iley/kamaji/demos/lcd/src/main.cpp

/*
  LiquidCrystal Library - Hello World
 
 Demonstrates the use a 16x2 LCD display.  The LiquidCrystal
 library works with all LCD displays that are compatible with the 
 Hitachi HD44780 driver. There are many of them out there, and you
 can usually tell them by the 16-pin interface.
 
 This sketch prints "Hello World!" to the LCD
 and shows the time.
 
  The circuit:
 * LCD RS pin to digital pin 12
 * LCD RW pin to digital pin 10
 * LCD Enable pin to digital pin 11
 * LCD D4 pin to digital pin 5
 * LCD D5 pin to digital pin 4
 * LCD D6 pin to digital pin 3
 * LCD D7 pin to digital pin 2
 * 10K resistor:
 * ends to +5V and ground
 * wiper to LCD VO pin (pin 3)
 
 Library originally added 18 Apr 2008
 by David A. Mellis
 library modified 5 Jul 2009
 by Limor Fried (http://www.ladyada.net)
 example added 9 Jul 2009
 by Tom Igoe
 modified 25 July 2009
 by David A. Mellis
 modified 25 May 2010
 by Ilya V. Danilov http://mk90.ru/

 */

// include the library code:
#include "Arduino.h"
#include <Wire.h>
#include <LiquidCrystal.h>

// initialize the library with the numbers of the interface pins
LiquidCrystal lcd(12, 11, 10, 9, 8, 7, 6);

void setup() {
  // set up the LCD's number of rows and columns: 
  lcd.begin(20, 4);
  // Print a message to the LCD.
  lcd.print("Привет, мир!");
}

void loop() {
  // set the cursor to column 0, line 1
  // (note: line 1 is the second row, since counting begins with 0):
  //lcd.setCursor(0, 1);
  // print the number of seconds since reset:
  lcd.print(millis()/1000);
  for (int k = 0; k < 5; k++) {
    for (int i = 0; i < 20; i++) {
      for (int j = 0; j < 4; j++) {
        if (k*80+j*20+i > 255)
          break;
        lcd.setCursor(i, j);
        lcd.write((unsigned char)(k*80 + j*20 + i));
      }
    }
    delay(2000);
  }
}
