iley/kamaji/demos/lcd12864/src/bitmap.h

#ifndef BITMAP_H
#define BITMAP_H

#define BITMAP_WIDTH 128
#define BITMAP_HEIGHT 64

#define BITMAP_DATA \
  0x00, 0x00, 0xC0, 0x00, 0x00, 0x00, 0x00, 0x00, 0x00, 0x00, 0x00, 0x00, \
  0x00, 0x00, 0x00, 0x00, 0x00, 0x00, 0xE0, 0x03, 0x00, 0x00, 0x00, 0x00, \
  0x00, 0x00, 0x00, 0x00, 0x00, 0x00, 0x00, 0x00, 0x00, 0x00, 0xF0, 0x03, \
  0x00, 0x00, 0x00, 0x00, 0x00, 0x00, 0x00, 0x00, 0x00, 0x00, 0x00, 0x00, \
  0x00, 0x00, 0x78, 0x06, 0x00, 0x00, 0x00, 0x00, 0x00, 0x00, 0x00, 0x00, \
  0x00, 0x00, 0x00, 0x00, 0x00, 0x00, 0x78, 0x0F, 0x00, 0x00, 0x00, 0x00, \
  0x00, 0x00, 0x00, 0x00, 0x00, 0x00, 0x00, 0x00, 0x00, 0x00, 0x78, 0x0C, \
  0x00, 0x00, 0x00, 0x00, 0x00, 0x00, 0x00, 0x00, 0x00, 0x00, 0x00, 0x00, \
  0x00, 0x00, 0x78, 0x1A, 0x00, 0x00, 0x00, 0x00, 0x00, 0x00, 0x00, 0x00, \
  0x00, 0x00, 0x00, 0x00, 0x78, 0x00, 0x98, 0x38, 0x00, 0x00, 0x00, 0x00, \
  0x00, 0x00, 0x00, 0x00, 0x00, 0x00, 0x00, 0x00, 0xFC, 0x00, 0x5C, 0x39, \
  0x00, 0x00, 0x00, 0x00, 0x00, 0x00, 0x00, 0x00, 0x00, 0x00, 0x00, 0x00, \
  0xDC, 0x01, 0x48, 0x72, 0x00, 0x00, 0x00, 0x00, 0x00, 0x00, 0x00, 0x00, \
  0x00, 0x00, 0x00, 0x00, 0x9C, 0x01, 0x58, 0x60, 0x00, 0x00, 0xF0, 0x03, \
  0x00, 0x00, 0x00, 0x00, 0x00, 0x00, 0x00, 0x00, 0xBE, 0x03, 0x9C, 0x62, \
  0x00, 0x00, 0xF8, 0x0F, 0x00, 0x00, 0x00, 0x00, 0x00, 0x00, 0x00, 0x00, \
  0x36, 0x07, 0x98, 0xE1, 0x00, 0x00, 0xBC, 0x1F, 0x00, 0x00, 0x00, 0x00, \
  0x00, 0x00, 0x00, 0x00, 0x26, 0x0E, 0x98, 0xC5, 0x01, 0x00, 0x0E, 0x0E, \
  0x00, 0x00, 0x00, 0x00, 0x00, 0x00, 0x00, 0x00, 0x66, 0x0C, 0x38, 0x87, \
  0x01, 0x00, 0x1C, 0x0E, 0x00, 0x00, 0x00, 0x00, 0x00, 0x00, 0x00, 0x00, \
  0x67, 0x1C, 0x30, 0x84, 0x03, 0x00, 0x1C, 0x07, 0x00, 0x00, 0x00, 0x00, \
  0x00, 0x00, 0x00, 0x00, 0x26, 0x18, 0x30, 0x04, 0x07, 0x00, 0x78, 0x07, \
  0x00, 0x00, 0x00, 0x00, 0x00, 0x00, 0x00, 0x00, 0xA6, 0x98, 0x7F, 0x06, \
  0x0E, 0x80, 0xFF, 0x03, 0xE0, 0x00, 0x00, 0x00, 0x00, 0x00, 0x00, 0x00, \
  0xA7, 0xF8, 0xBF, 0x01, 0x1C, 0xC0, 0xFF, 0x03, 0xE0, 0x03, 0x00, 0x00, \
  0x00, 0x00, 0x00, 0x00, 0xC6, 0xF1, 0x64, 0x00, 0x18, 0xC0, 0xE7, 0x01, \
  0xC0, 0x0F, 0x00, 0x00, 0x00, 0x00, 0x00, 0x00, 0x4E, 0x31, 0x17, 0x00, \
  0x38, 0x00, 0xC0, 0x01, 0xC0, 0x3F, 0x00, 0x00, 0x00, 0x00, 0x00, 0x00, \
  0x8C, 0xA1, 0x00, 0x00, 0x30, 0x00, 0xE0, 0x00, 0xE0, 0xFC, 0x00, 0x00, \
  0x00, 0x00, 0x00, 0x00, 0x8C, 0x43, 0x00, 0x00, 0x70, 0x00, 0xE0, 0x00, \
  0xE0, 0xF0, 0x01, 0x00, 0x00, 0x00, 0x00, 0x00, 0x18, 0x02, 0x00, 0x00, \
  0x60, 0x00, 0x40, 0x00, 0x70, 0xC0, 0x03, 0x00, 0x00, 0x00, 0x00, 0x00, \
  0x38, 0x02, 0x00, 0x00, 0xE0, 0x00, 0x00, 0x00, 0x70, 0xE0, 0x03, 0x00, \
  0x00, 0x00, 0x00, 0x00, 0x30, 0x02, 0x00, 0x00, 0xC0, 0x00, 0x00, 0x00, \
  0x38, 0xF0, 0x00, 0x00, 0x00, 0x00, 0x00, 0x00, 0x70, 0x02, 0x00, 0x00, \
  0xC0, 0x01, 0x00, 0x00, 0x1C, 0x70, 0x00, 0x00, 0x00, 0x00, 0x00, 0x00, \
  0xE0, 0x03, 0x00, 0x00, 0x80, 0x01, 0x00, 0x00, 0x1C, 0x30, 0x00, 0x00, \
  0x00, 0x00, 0x00, 0x00, 0x60, 0x02, 0x00, 0x00, 0x80, 0x01, 0x00, 0x00, \
  0x0E, 0x38, 0x00, 0x04, 0x00, 0x00, 0x00, 0x00, 0x60, 0x00, 0x00, 0x00, \
  0x80, 0x01, 0x00, 0x00, 0x0E, 0x38, 0x80, 0x07, 0x00, 0x00, 0x00, 0x00, \
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

#endif //BITMAP_H
