iley/kamaji/demos/tetris/pack_tetrominoes.py

#!/usr/bin/env python
from __future__ import print_function


def pack_tetrominoes():
    for tetromino in tetrominoes:
        print("  {")
        for rotation in tetromino:
            word = 0
            for row in reversed(rotation):
                for digit in reversed(row):
                    word = (word << 1) | digit
            hex_word = '0x' + hex(word)[2:].zfill(4)
            print("    %s," % hex_word)
        print("  },")


tetrominoes = [
  # O
  [
    [
      [0, 0, 0, 0],
      [0, 1, 1, 0],
      [0, 1, 1, 0],
      [0, 0, 0, 0],
    ],
    [
      [0, 0, 0, 0],
      [0, 1, 1, 0],
      [0, 1, 1, 0],
      [0, 0, 0, 0],
    ],
    [
      [0, 0, 0, 0],
      [0, 1, 1, 0],
      [0, 1, 1, 0],
      [0, 0, 0, 0],
    ],
    [
      [0, 0, 0, 0],
      [0, 1, 1, 0],
      [0, 1, 1, 0],
      [0, 0, 0, 0],
    ],
  ],

  # I
  [
    [
      [0, 0, 0, 0],
      [1, 1, 1, 1],
      [0, 0, 0, 0],
      [0, 0, 0, 0],
    ],
    [
      [0, 0, 1, 0],
      [0, 0, 1, 0],
      [0, 0, 1, 0],
      [0, 0, 1, 0],
    ],
    [
      [0, 0, 0, 0],
      [1, 1, 1, 1],
      [0, 0, 0, 0],
      [0, 0, 0, 0],
    ],
    [
      [0, 0, 1, 0],
      [0, 0, 1, 0],
      [0, 0, 1, 0],
      [0, 0, 1, 0],
    ],
  ],

  # J
  [
    [
      [1, 0, 0, 0],
      [1, 1, 1, 0],
      [0, 0, 0, 0],
      [0, 0, 0, 0],
    ],
    [
      [0, 1, 1, 0],
      [0, 1, 0, 0],
      [0, 1, 0, 0],
      [0, 0, 0, 0],
    ],
    [
      [0, 0, 0, 0],
      [1, 1, 1, 0],
      [0, 0, 1, 0],
      [0, 0, 0, 0],
    ],
    [
      [0, 1, 0, 0],
      [0, 1, 0, 0],
      [1, 1, 0, 0],
      [0, 0, 0, 0],
    ],
  ],

  # L
  [
    [
      [0, 0, 1, 0],
      [1, 1, 1, 0],
      [0, 0, 0, 0],
      [0, 0, 0, 0],
    ],
    [
      [0, 1, 0, 0],
      [0, 1, 0, 0],
      [0, 1, 1, 0],
      [0, 0, 0, 0],
    ],
    [
      [0, 0, 0, 0],
      [1, 1, 1, 0],
      [1, 0, 0, 0],
      [0, 0, 0, 0],
    ],
    [
      [1, 1, 0, 0],
      [0, 1, 0, 0],
      [0, 1, 0, 0],
      [0, 0, 0, 0],
    ],
  ],

  # S
  [
    [
      [0, 1, 1, 0],
      [1, 1, 0, 0],
      [0, 0, 0, 0],
      [0, 0, 0, 0],
    ],
    [
      [0, 1, 0, 0],
      [0, 1, 1, 0],
      [0, 0, 1, 0],
      [0, 0, 0, 0],
    ],
    [
      [0, 0, 0, 0],
      [0, 1, 1, 0],
      [1, 1, 0, 0],
      [0, 0, 0, 0],
    ],
    [
      [1, 0, 0, 0],
      [1, 1, 0, 0],
      [0, 1, 0, 0],
      [0, 0, 0, 0],
    ],
  ],

  # Z
  [
    [
      [1, 1, 0, 0],
      [0, 1, 1, 0],
      [0, 0, 0, 0],
      [0, 0, 0, 0],
    ],
    [
      [0, 0, 1, 0],
      [0, 1, 1, 0],
      [0, 1, 0, 0],
      [0, 0, 0, 0],
    ],
    [
      [0, 0, 0, 0],
      [1, 1, 0, 0],
      [0, 1, 1, 0],
      [0, 0, 0, 0],
    ],
    [
      [0, 1, 0, 0],
      [1, 1, 0, 0],
      [1, 0, 0, 0],
      [0, 0, 0, 0],
    ],
  ],

  # T
  [
    [
      [0, 1, 0, 0],
      [1, 1, 1, 0],
      [0, 0, 0, 0],
      [0, 0, 0, 0],
    ],
    [
      [0, 1, 0, 0],
      [0, 1, 1, 0],
      [0, 1, 0, 0],
      [0, 0, 0, 0],
    ],
    [
      [0, 0, 0, 0],
      [1, 1, 1, 0],
      [0, 1, 0, 0],
      [0, 0, 0, 0],
    ],
    [
      [0, 1, 0, 0],
      [1, 1, 0, 0],
      [0, 1, 0, 0],
      [0, 0, 0, 0],
    ],
  ],
]

if __name__ == "__main__":
    pack_tetrominoes()
